padamsarda/feather-SAMD21-WD/images/WhatsApp Image 2026-07-10 at 05.25.07.jpeg

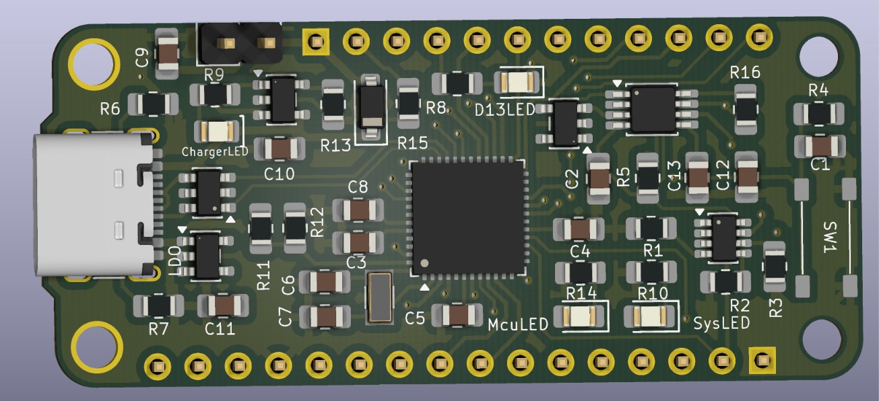
images/WhatsApp Image 2026-07-10 at 05.25.07.jpeg
